jcarlosfernando/Q-Robot/STLs_Q-Robot/R_Paw_Cover.stl

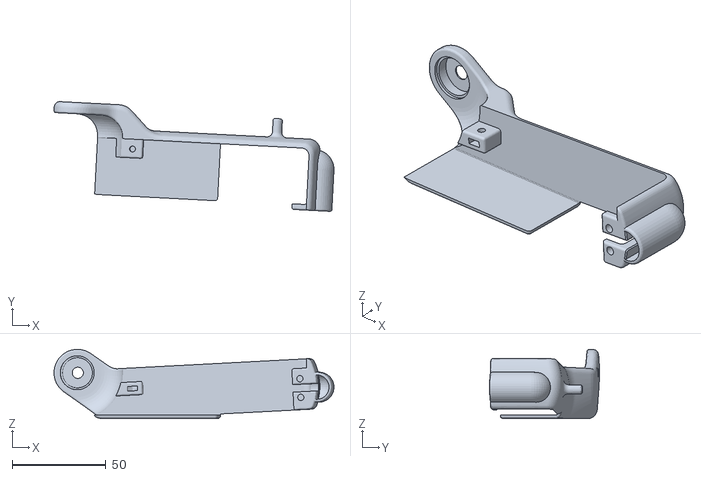
[picture p15: CAD file, 2022-07-06]
STLs_Q-Robot/R_Paw_Cover.stl
149.5 x 58.6 x 37.0
