jcarlosfernando/Q-Robot/STLs_Q-Robot/Cover_Lower.stl

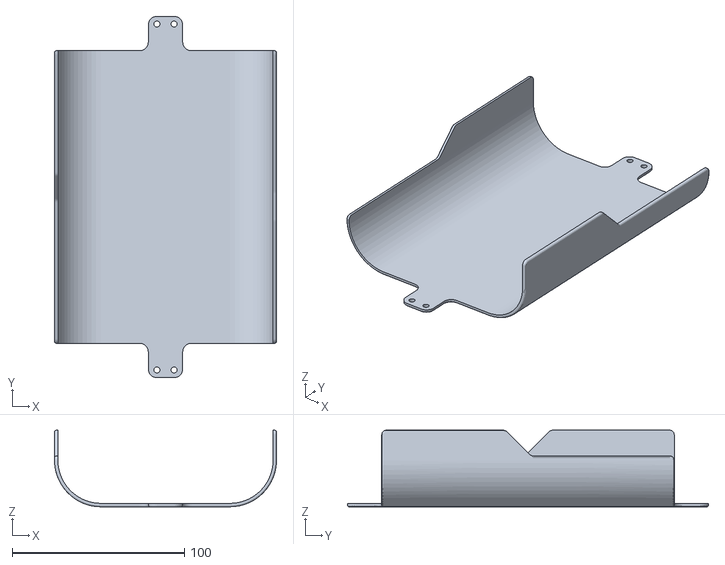
[picture p16: CAD file, 2022-07-06]
STLs_Q-Robot/Cover_Lower.stl
129.0 x 210.0 x 44.5
