jcarlosfernando/Q-Robot/STLs_Q-Robot/Inter_Part2.stl

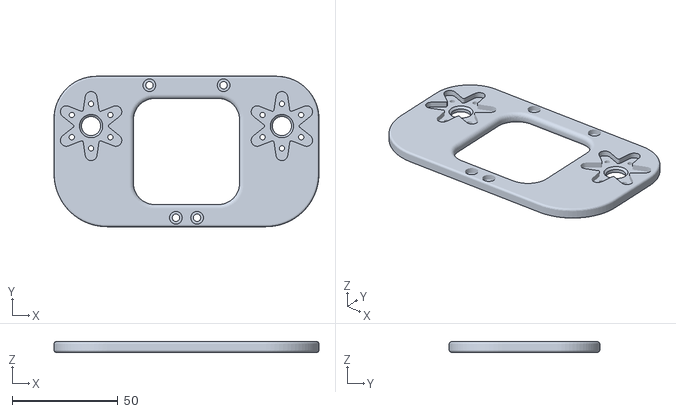
[picture p17: CAD file, 2022-07-06]
STLs_Q-Robot/Inter_Part2.stl
125.0 x 71.0 x 5.00
